canardos/bake-n-flow/src/ui/ui_common.h

#ifndef UI_UI_COMMON_H_
#define UI_UI_COMMON_H_

#include "ui/ui_defs.h"
#include "ui/ui_styles.h"
#include "ui/ui_page.h"
#include "ui/ui_modal.h"
#include "ui/lvgl_tools.h"


#endif /* UI_UI_COMMON_H_ */
